MaykerBel1712/Weather-Energy-Node/docs/Actuador/PCB Actuador.jpeg

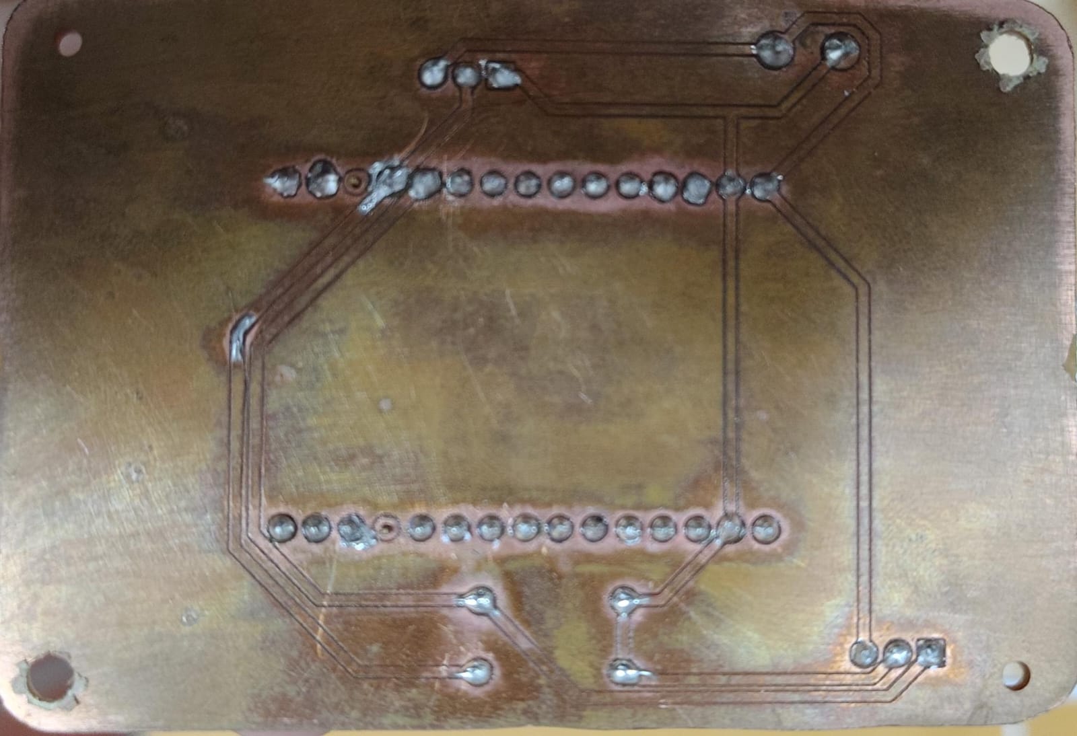
docs/Actuador/PCB Actuador.jpeg
