MaykerBel1712/Weather-Energy-Node/docs/Actuador/Sistema Actuador.jpeg

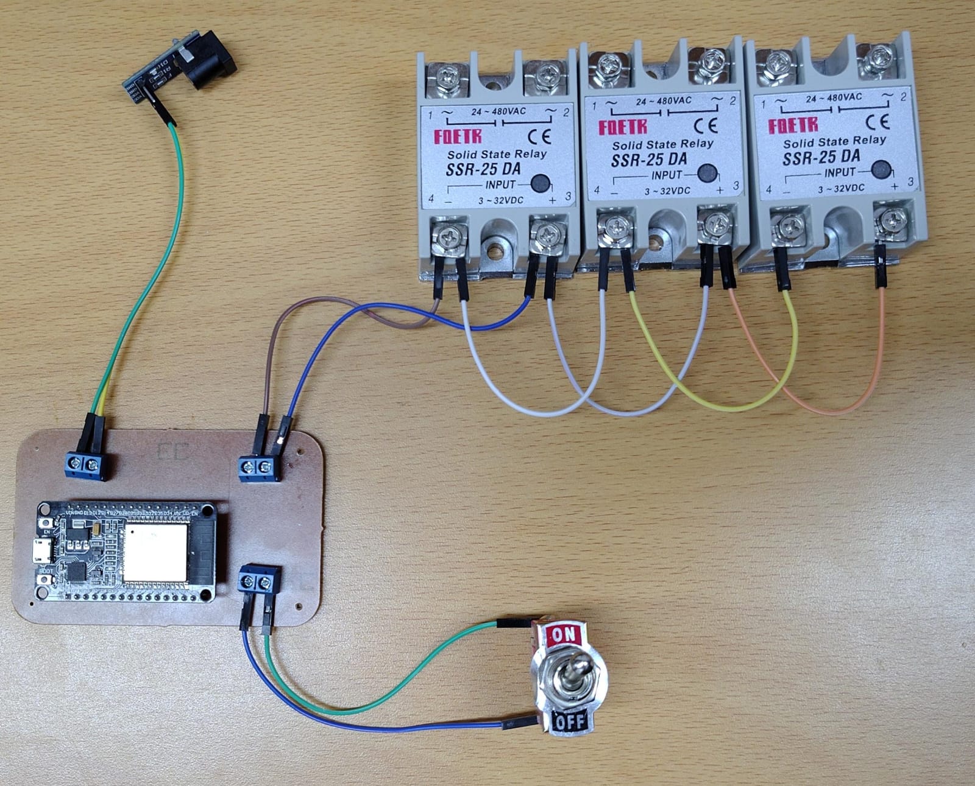
docs/Actuador/Sistema Actuador.jpeg
