MaykerBel1712/Weather-Energy-Node/docs/Detector/Prototipo Deteccion.jpeg

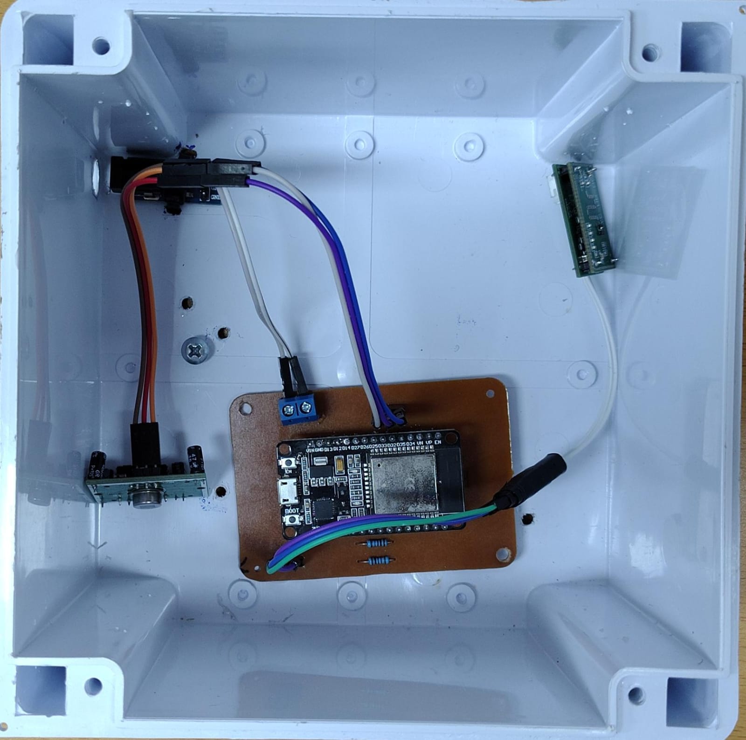
docs/Detector/Prototipo Deteccion.jpeg
