MaykerBel1712/Weather-Energy-Node/docs/Detector/Sistema Deteccion.jpeg

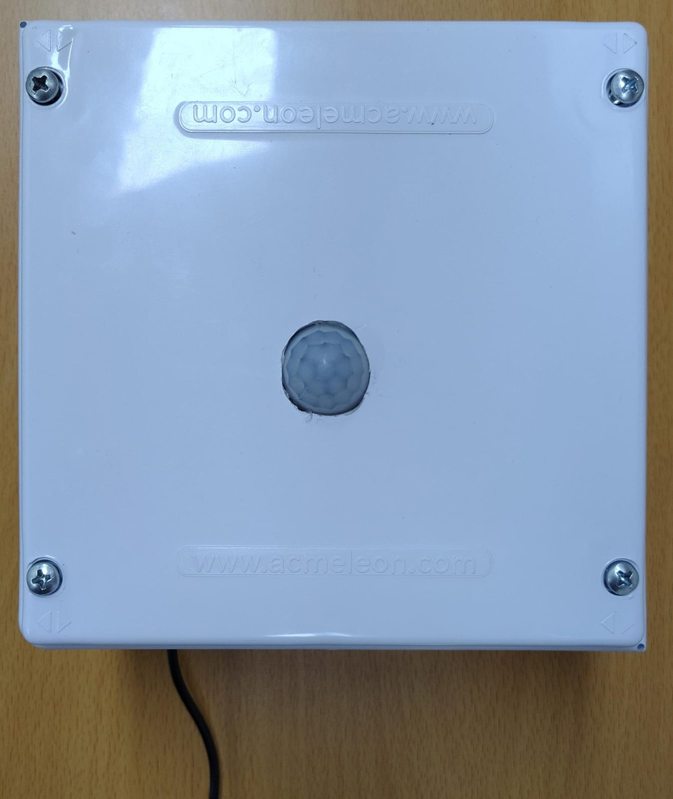
docs/Detector/Sistema Deteccion.jpeg
