MaykerBel1712/Weather-Energy-Node/docs/Energía/1.jpg

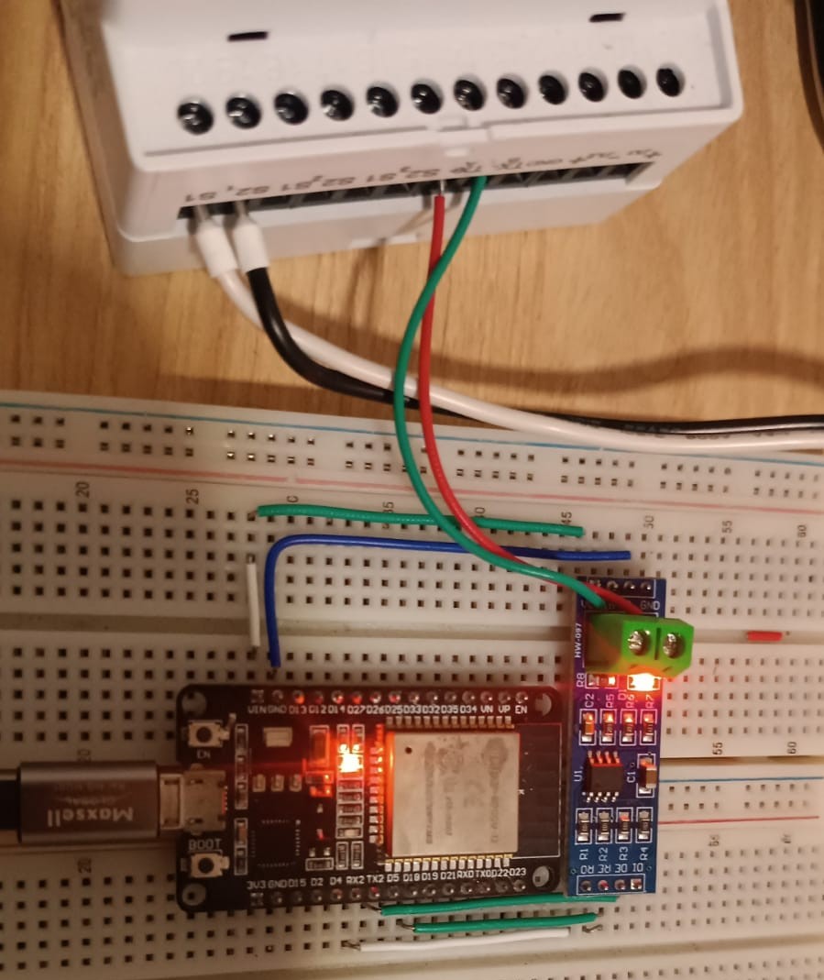
docs/Energía/1.jpg
