MaykerBel1712/Weather-Energy-Node/docs/Energía/2.jpg

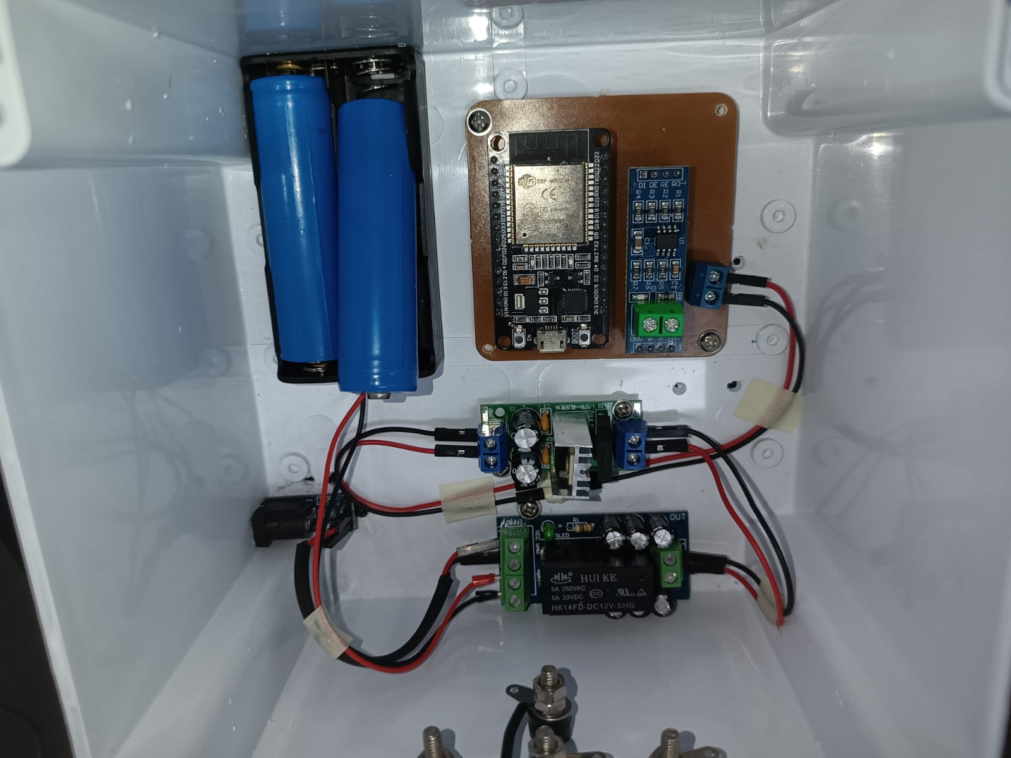
docs/Energía/2.jpg
