MaykerBel1712/Weather-Energy-Node/docs/Energía/3.jpg

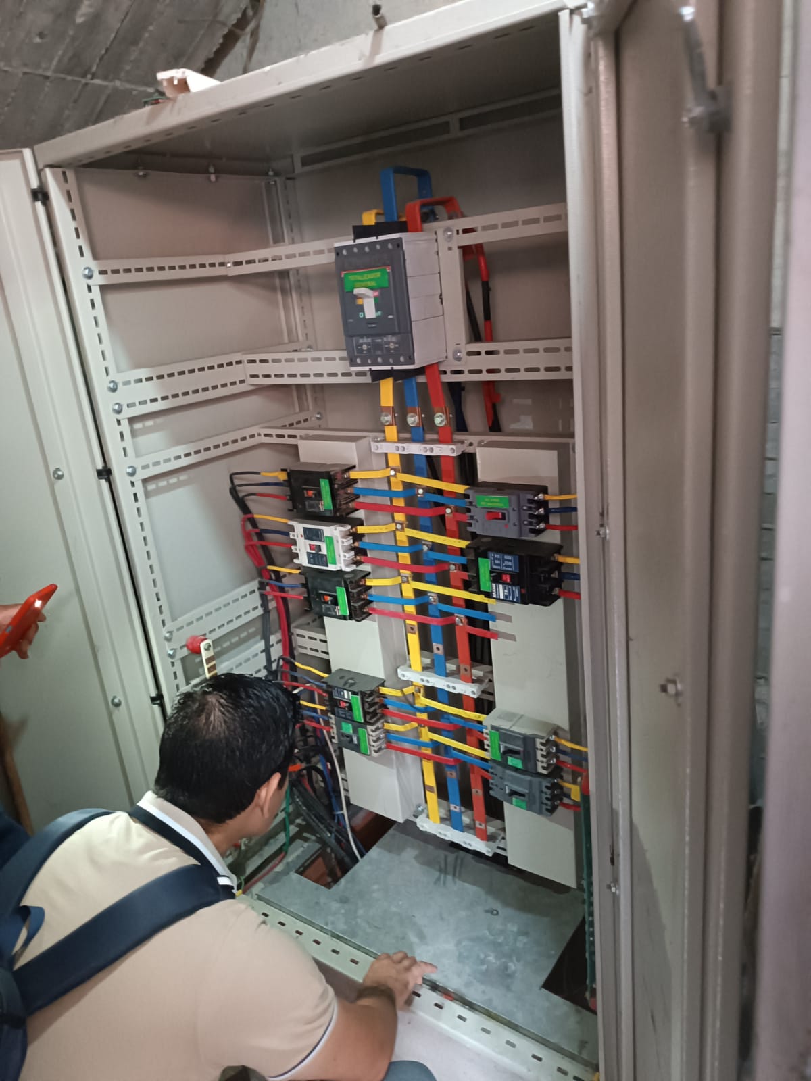
docs/Energía/3.jpg
