MaykerBel1712/Weather-Energy-Node/docs/Energía/4.jpg

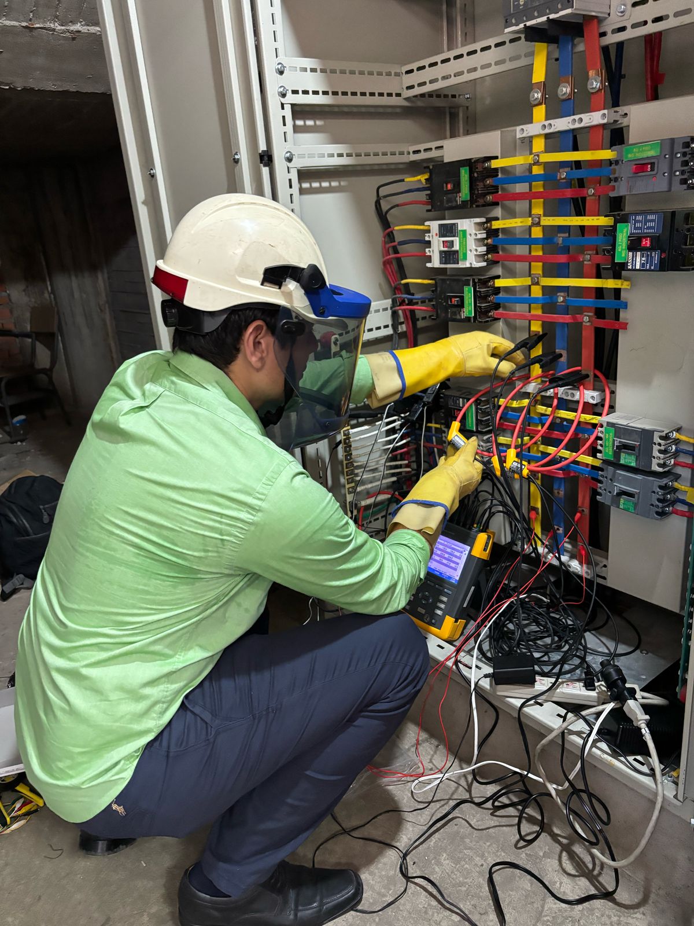
docs/Energía/4.jpg
