MaykerBel1712/Weather-Energy-Node/docs/Meteorología/cinco.jpg

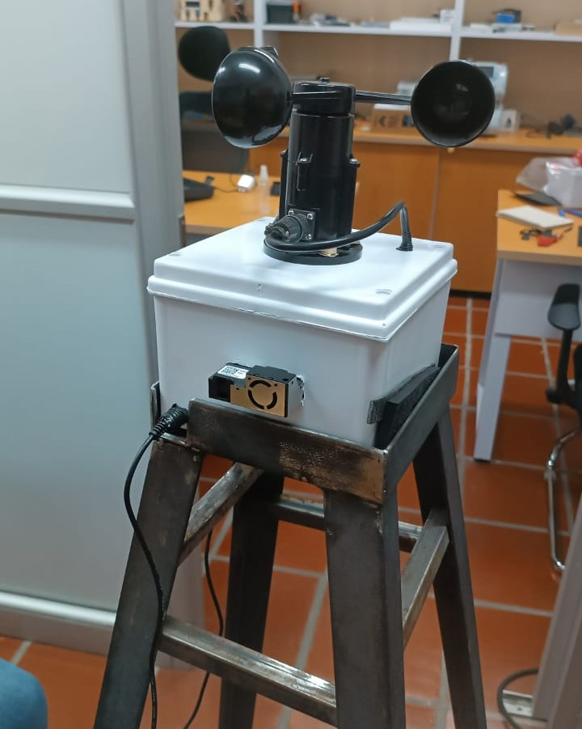
docs/Meteorología/cinco.jpg
