MaykerBel1712/Weather-Energy-Node/docs/Meteorología/conexion servidor.png

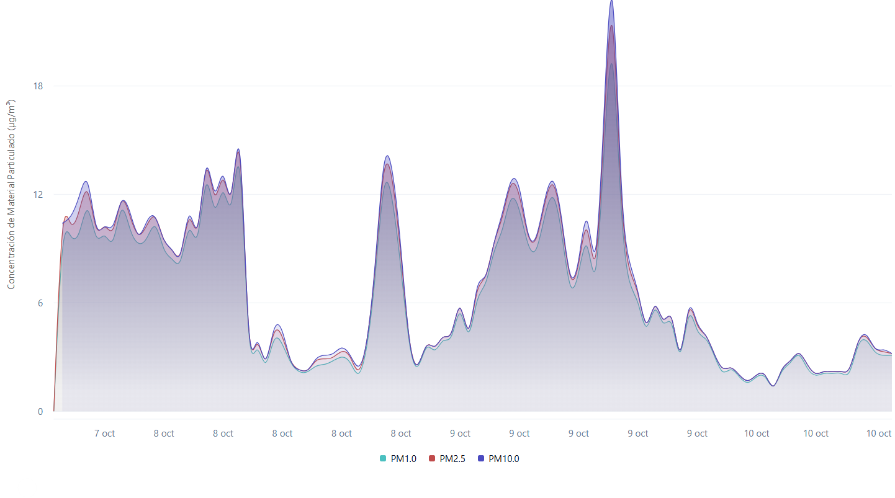
docs/Meteorología/conexion servidor.png
