MaykerBel1712/Weather-Energy-Node/docs/Meteorología/estacionmeteo1.jpg

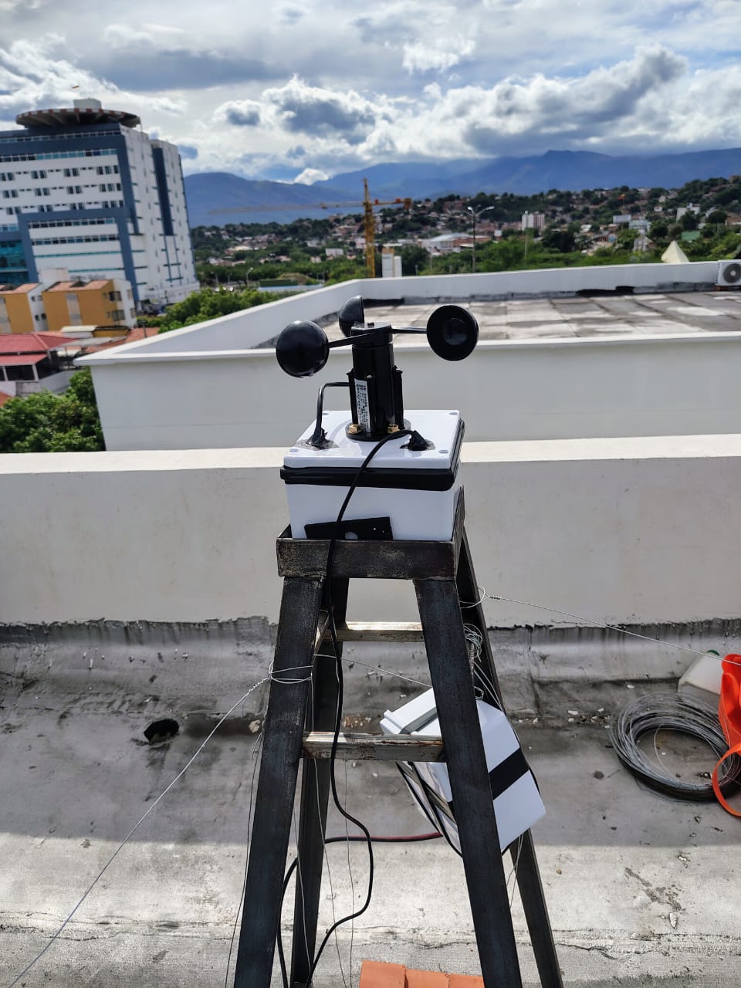
docs/Meteorología/estacionmeteo1.jpg
