MaykerBel1712/Weather-Energy-Node/docs/Meteorología/estacionmeteo2.jpg

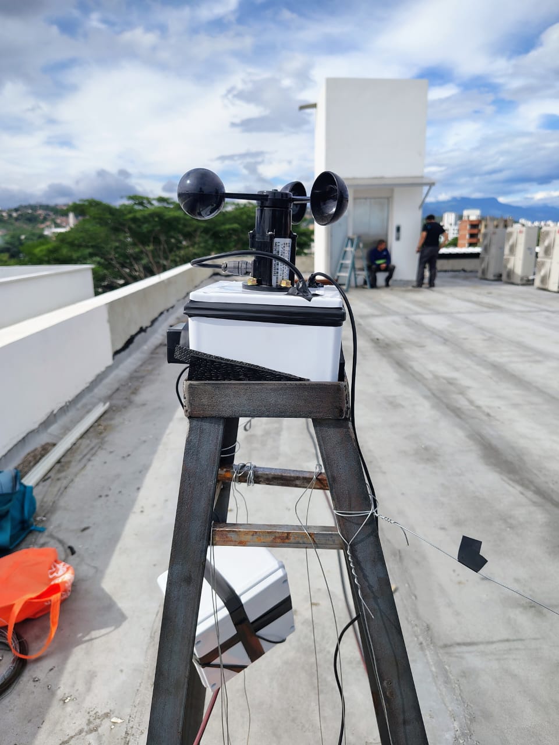
docs/Meteorología/estacionmeteo2.jpg
