MaykerBel1712/Weather-Energy-Node/docs/Meteorología/uno.jpg

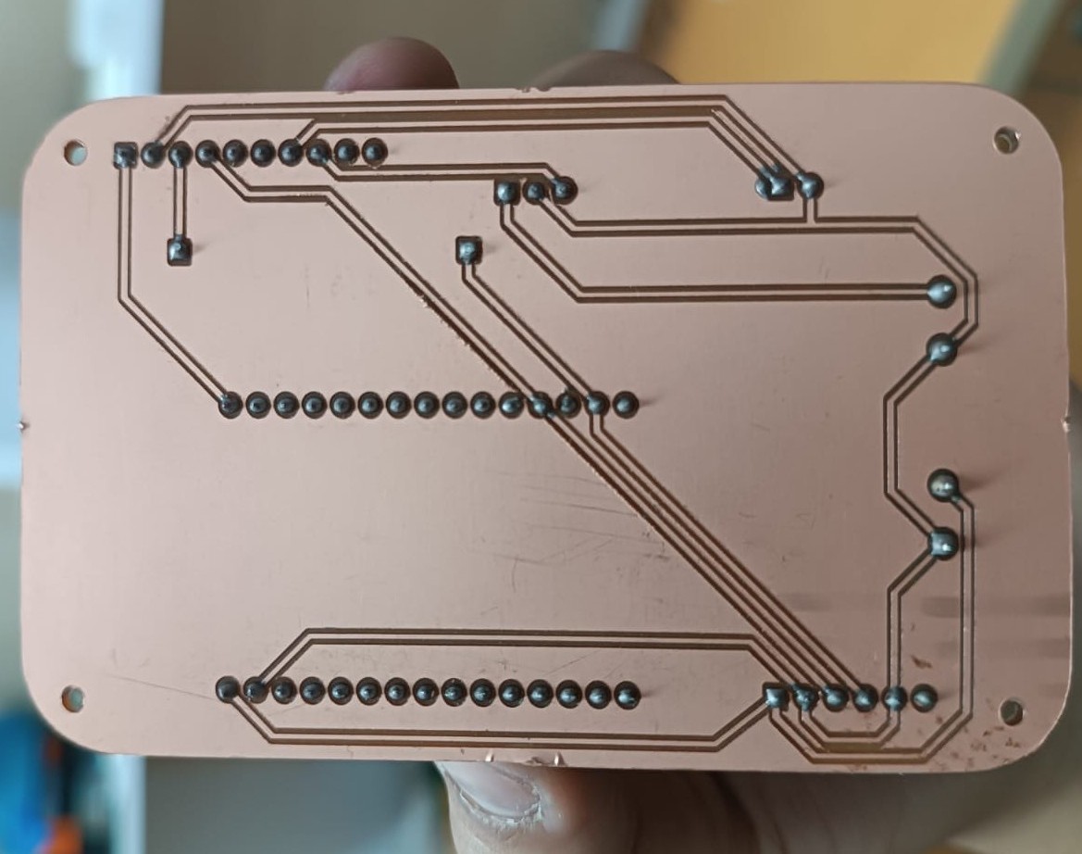
docs/Meteorología/uno.jpg
