MaykerBel1712/Weather-Energy-Node/docs/Pcbs/Domótica/PCB 3D Frontal.png

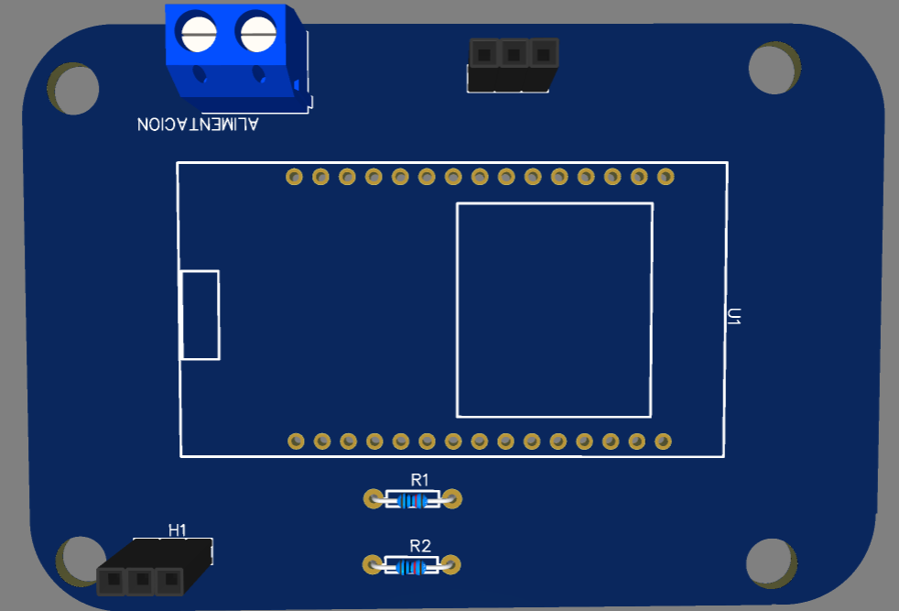
docs/Pcbs/Domótica/PCB 3D Frontal.png
