MaykerBel1712/Weather-Energy-Node/docs/Pcbs/Domótica/PCB 3D Traasera Actuador.png

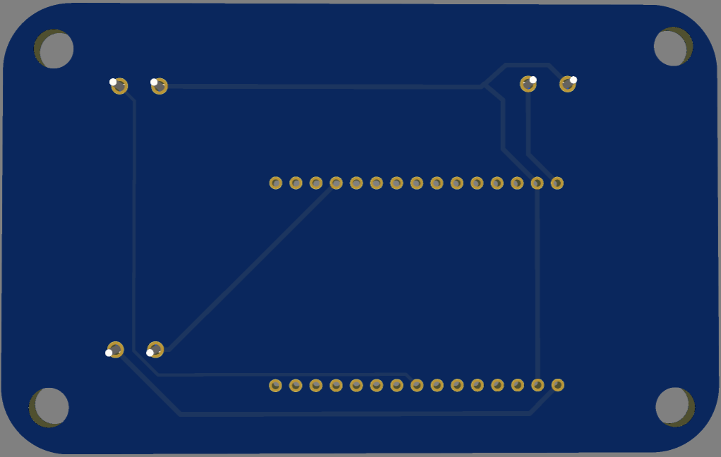
docs/Pcbs/Domótica/PCB 3D Traasera Actuador.png
