MaykerBel1712/Weather-Energy-Node/docs/Pcbs/Domótica/PCB 3D Trasera.png

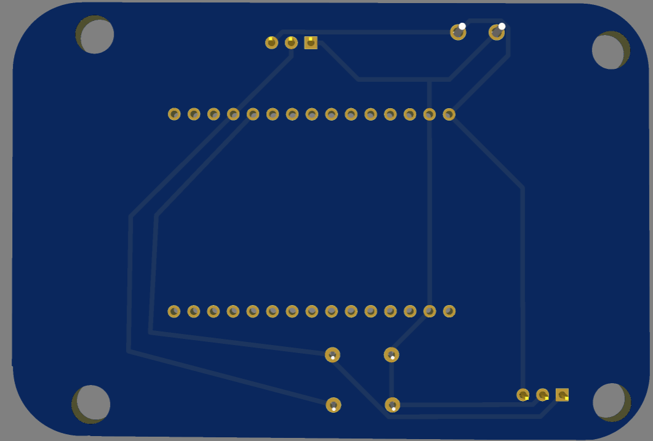
docs/Pcbs/Domótica/PCB 3D Trasera.png
