MaykerBel1712/Weather-Energy-Node/docs/Pcbs/Energía/3DFrontalEnergía.png

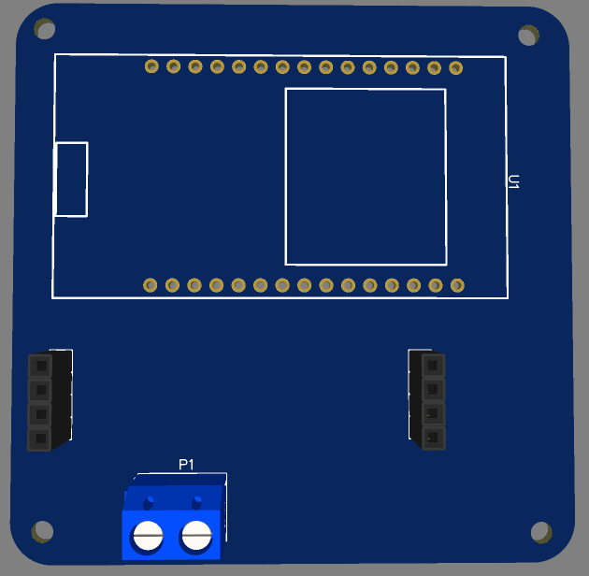
docs/Pcbs/Energía/3DFrontalEnergía.png
