MaykerBel1712/Weather-Energy-Node/docs/Pcbs/Energía/3DTraseraEnergía.png

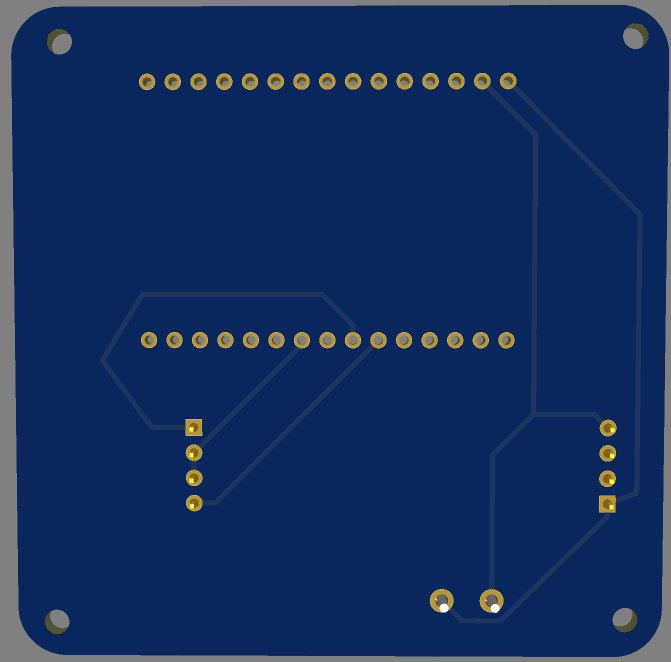
docs/Pcbs/Energía/3DTraseraEnergía.png
