MaykerBel1712/Weather-Energy-Node/docs/Pcbs/Mateorología/3DFrontalMeteo.png

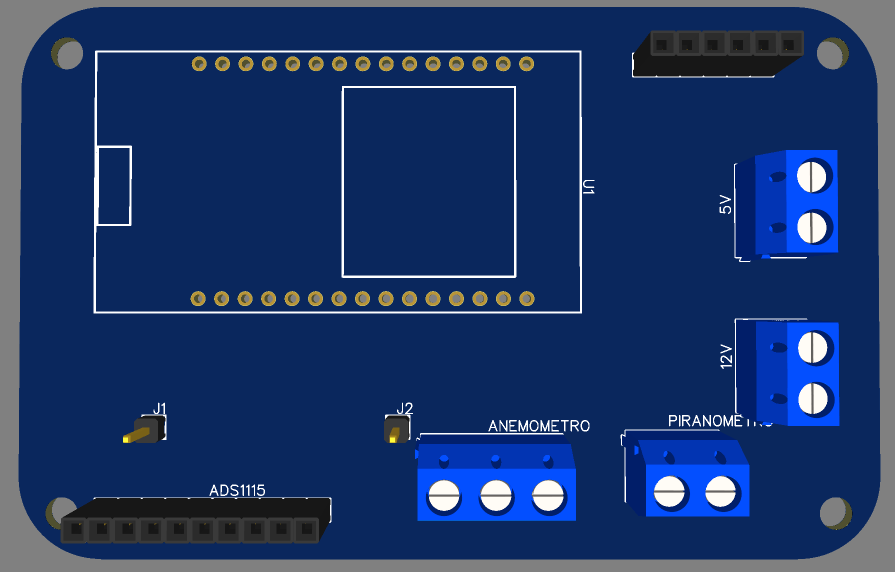
docs/Pcbs/Mateorología/3DFrontalMeteo.png
