MaykerBel1712/Weather-Energy-Node/docs/Pcbs/Mateorología/3DTraseraMeteo.png

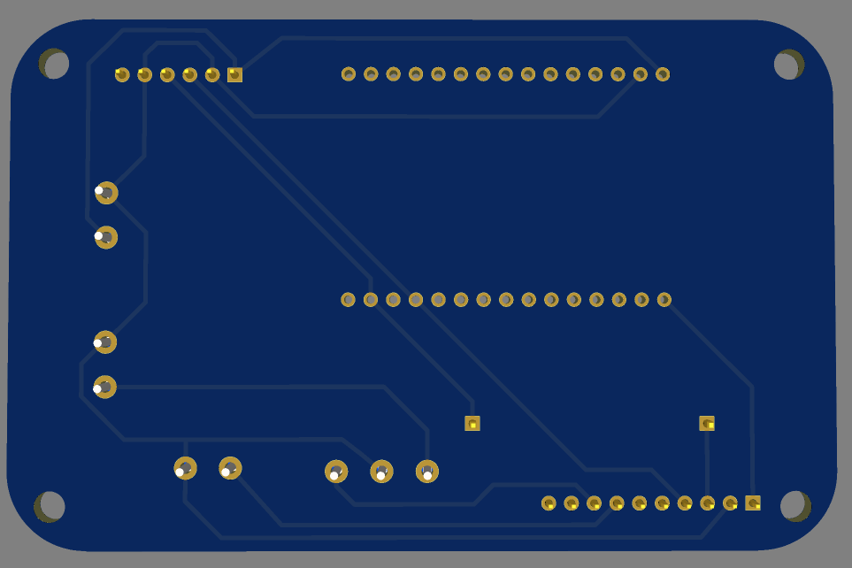
docs/Pcbs/Mateorología/3DTraseraMeteo.png
