MaykerBel1712/Weather-Energy-Node/docs/Ponencia.jpeg

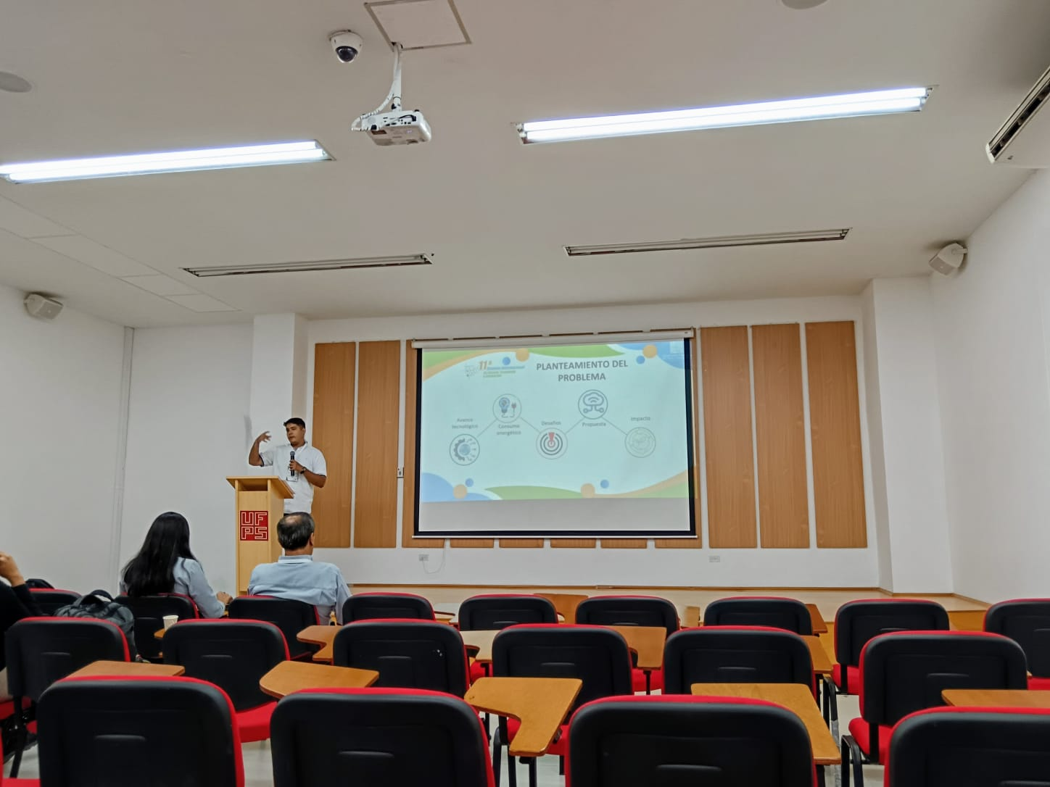
docs/Ponencia.jpeg
