MaykerBel1712/Weather-Energy-Node/docs/Página/creditos.png

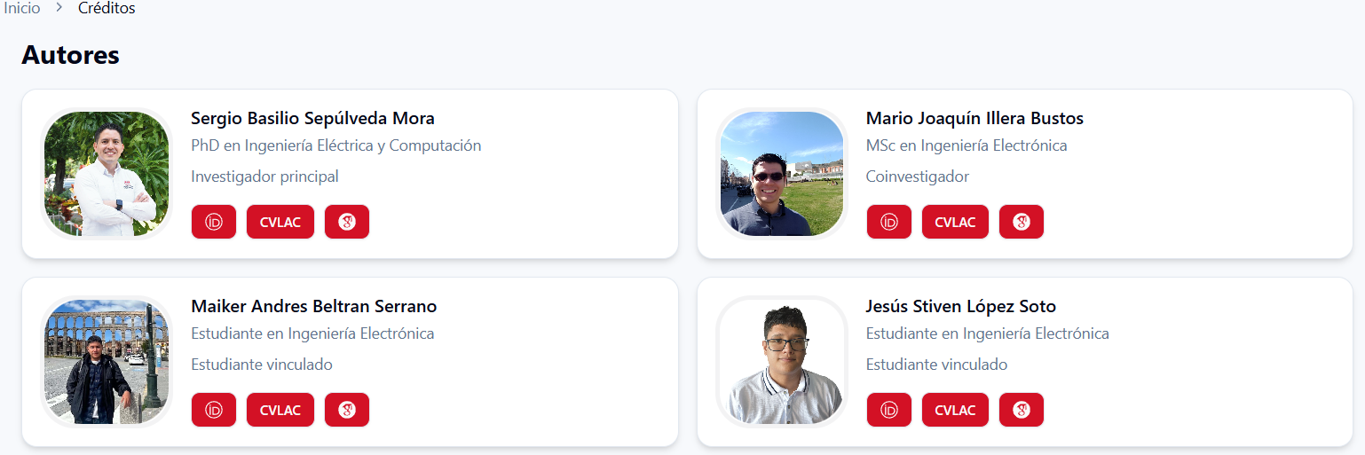
docs/Página/creditos.png
