MaykerBel1712/Weather-Energy-Node/docs/Página/DASHBOARDENERGIA.JPG

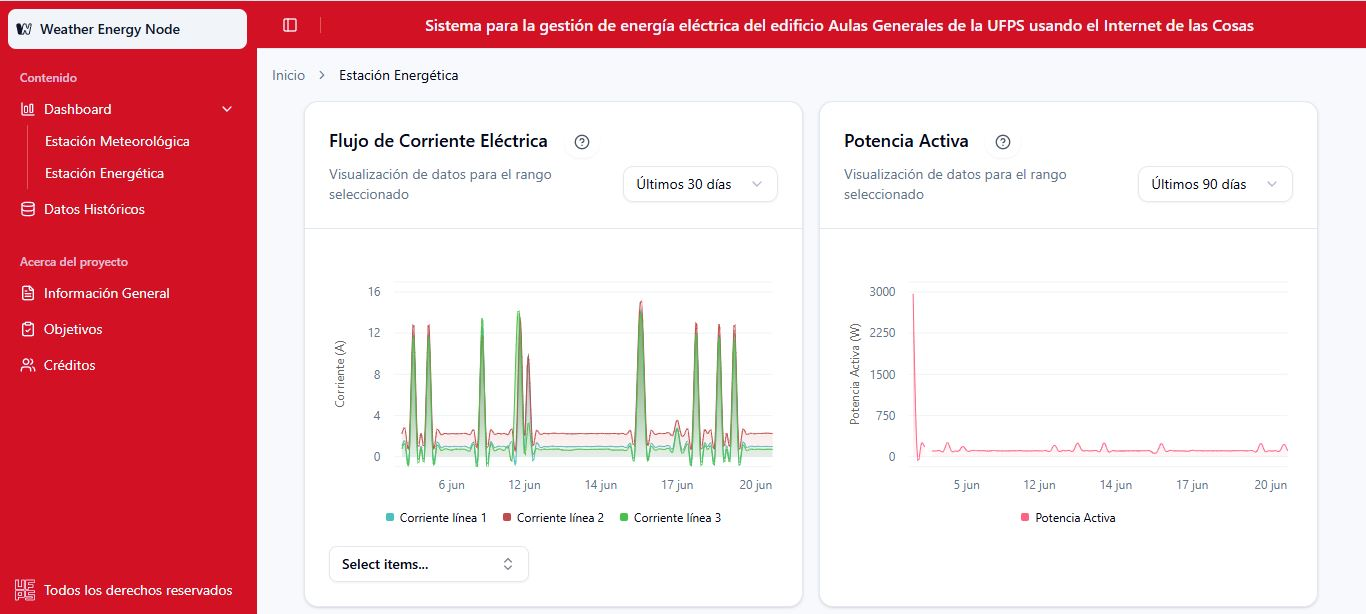
docs/Página/DASHBOARDENERGIA.JPG
