MaykerBel1712/Weather-Energy-Node/docs/Página/DASHBOARDMETEOROLOGIA.JPG

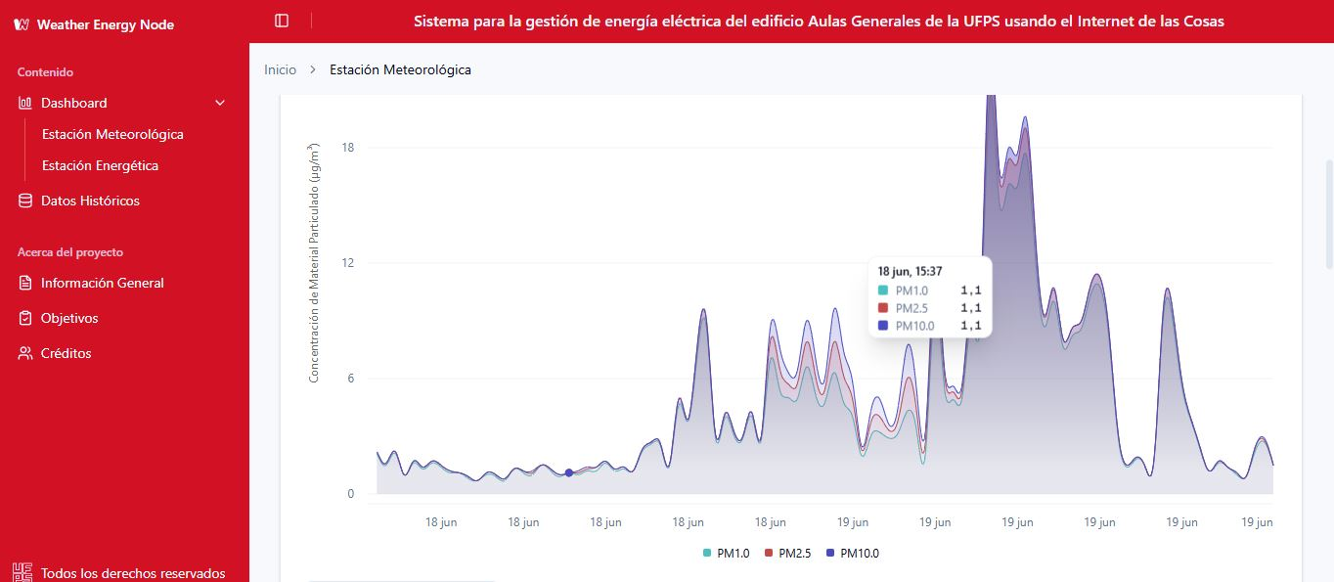
docs/Página/DASHBOARDMETEOROLOGIA.JPG
