MaykerBel1712/Weather-Energy-Node/docs/Página/database.JPG

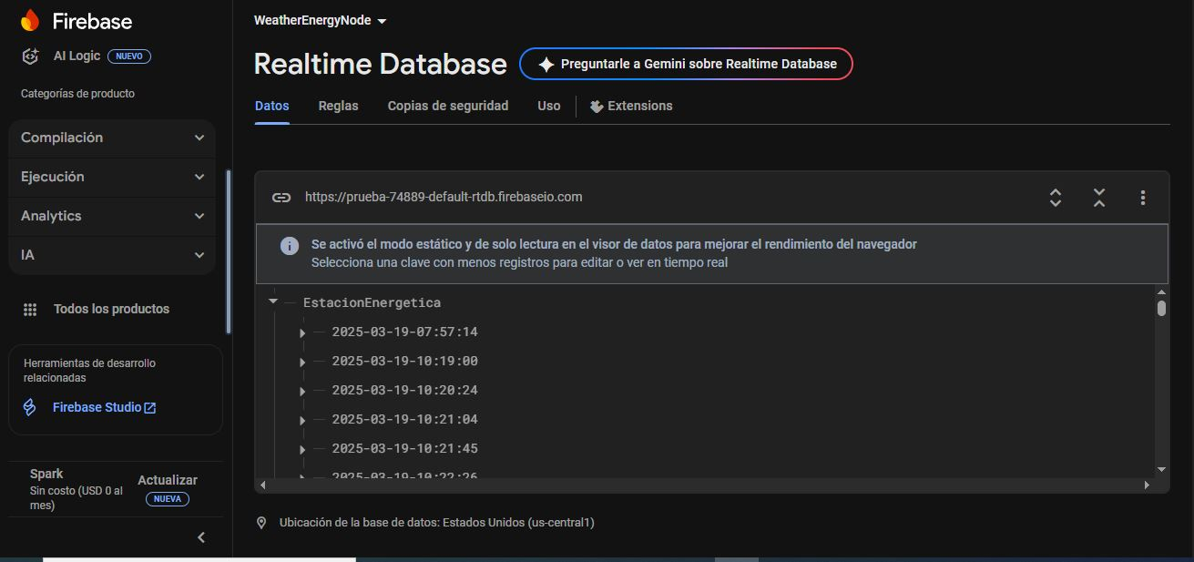
docs/Página/database.JPG
