MaykerBel1712/Weather-Energy-Node/docs/Página/HISTORICOS.JPG

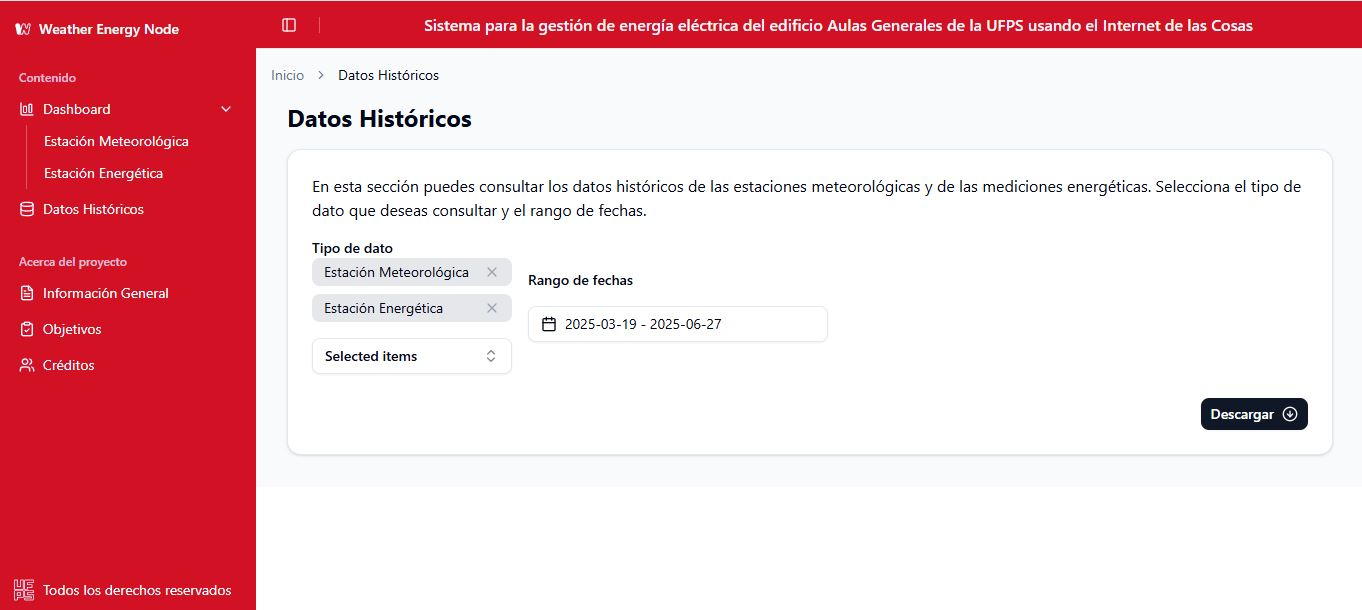
docs/Página/HISTORICOS.JPG
