MaykerBel1712/Weather-Energy-Node/docs/Página/HISTORICOS.png

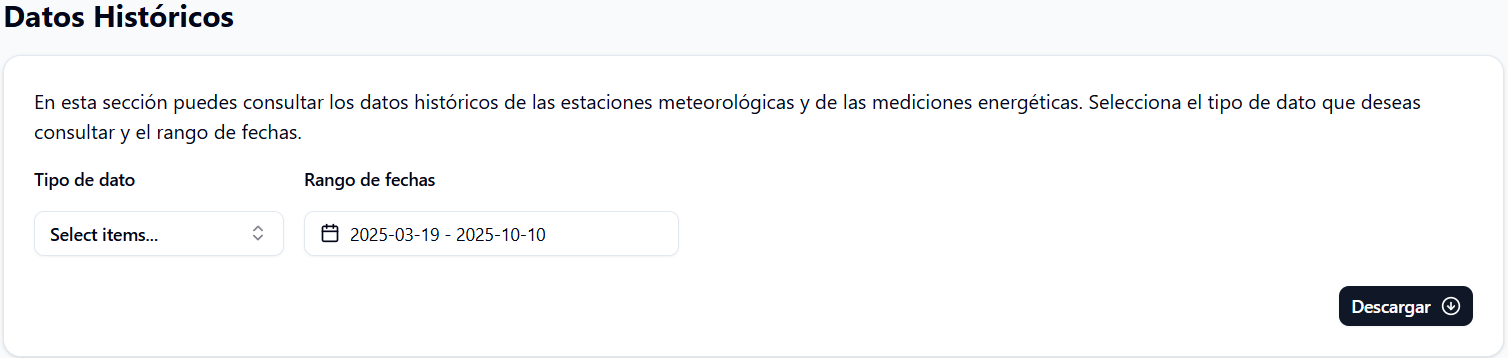
docs/Página/HISTORICOS.png
